eyalabraham/incidence-meter/doc/IMG_3270.JPG

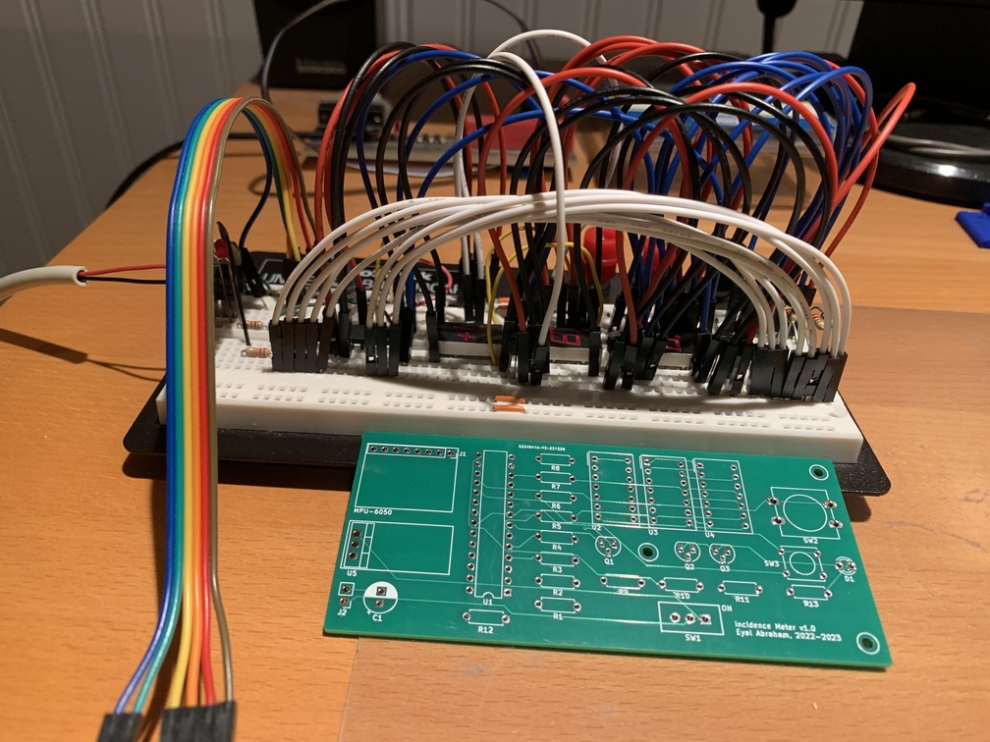
doc/IMG_3270.JPG
