eyalabraham/incidence-meter/doc/IMG_3272.jpg

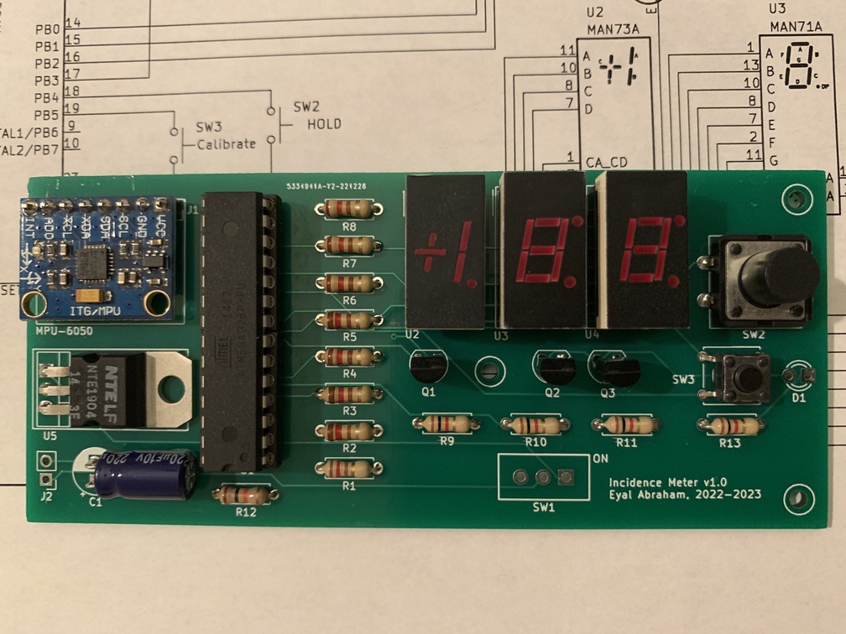
doc/IMG_3272.jpg
