eyalabraham/incidence-meter/doc/IMG_3273.jpg

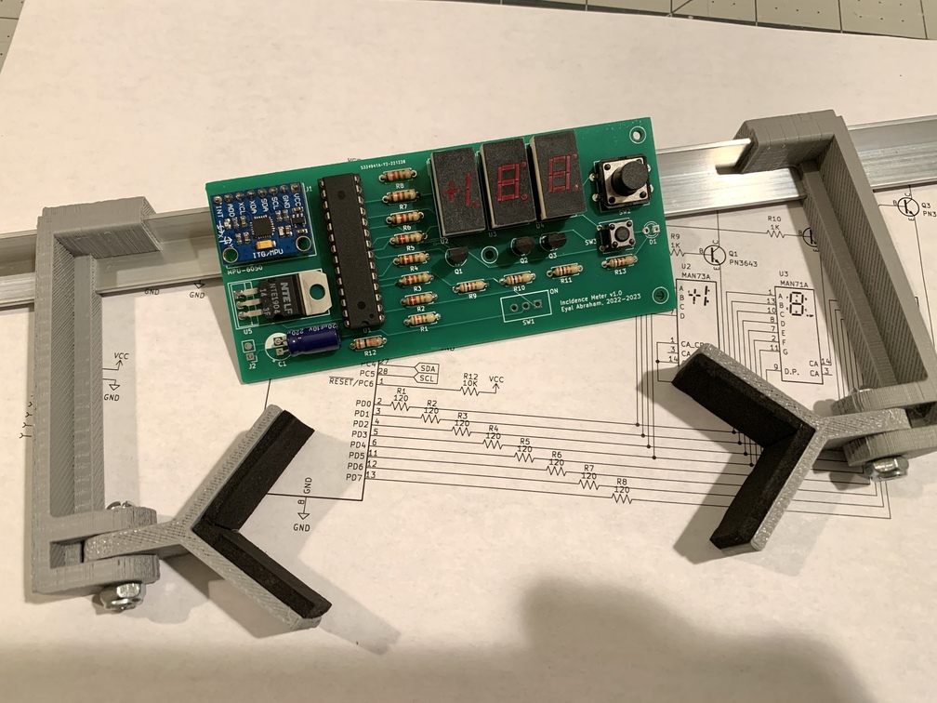
doc/IMG_3273.jpg
